DanielHLelis/fonte-tensao-ajustavel-ssc180/schematics/schem-v1.sch

## EAGLE design schematics/schem-v1.sch (2021-07-29)

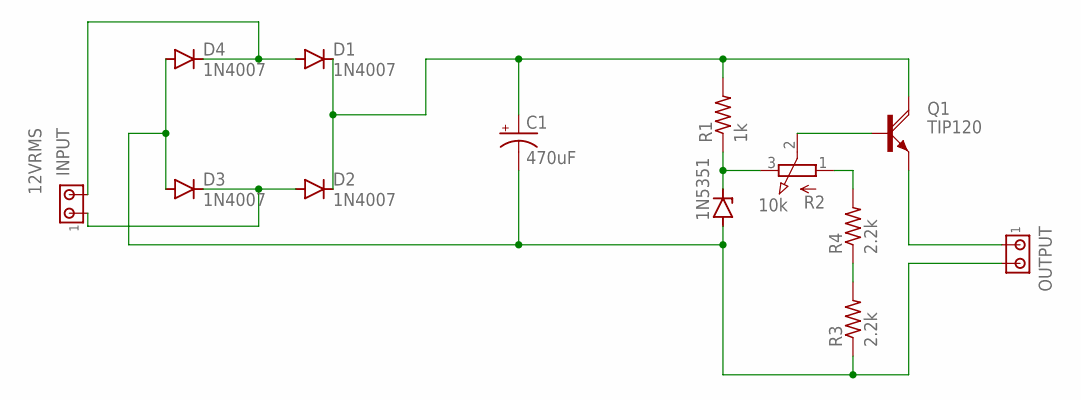
[picture p3: schematic schem-v1.sch]

Parts:
1N5351: ZENER-DIODEDO41Z10; DO41Z10
C1: 470uF; E3,5-10
D1, D2, D3, D4: 1N4007; DO41-10
INPUT: 12VRMS; 10X02MTA
OUTPUT: MTA02-100; 10X02MTA
Q1: TIP120; TO220AH
R1: 1k; 0207/10
R2: 10k; 3RP/1610N
R3, R4: 2.2k; 0207/10

Connections:
GND: 1N5351.A, C1.-, D3.A, D4.A, OUTPUT.2, R3.1
unnamed: D1.A, D4.C, INPUT.2
unnamed: D2.A, D3.C, INPUT.1
unnamed: 1N5351.C, R1.1, R2.3 (E)
unnamed: R2.1 (A), R4.2
unnamed: R3.2, R4.1
unnamed: Q1.B, R2.2 (S)
unnamed: OUTPUT.1, Q1.E
VCC: C1.+, D1.C, D2.C, Q1.C, R1.2
